gojimmypi/IoT_BBQ/Assignments/images/missing_mcu_families.png

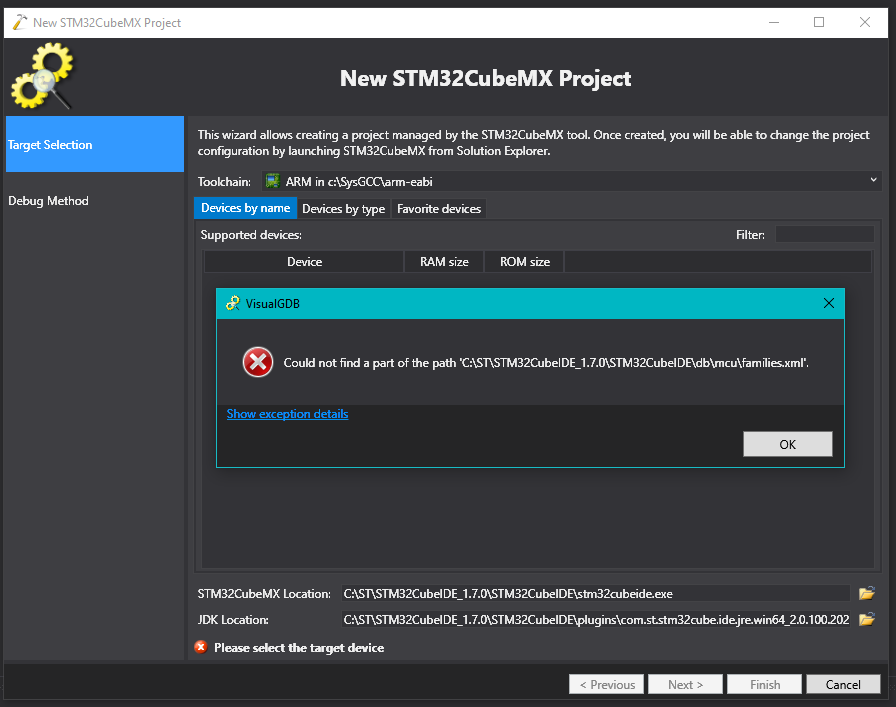
Assignments/images/missing_mcu_families.png
