gojimmypi/IoT_BBQ/pics/blinky_pins.png

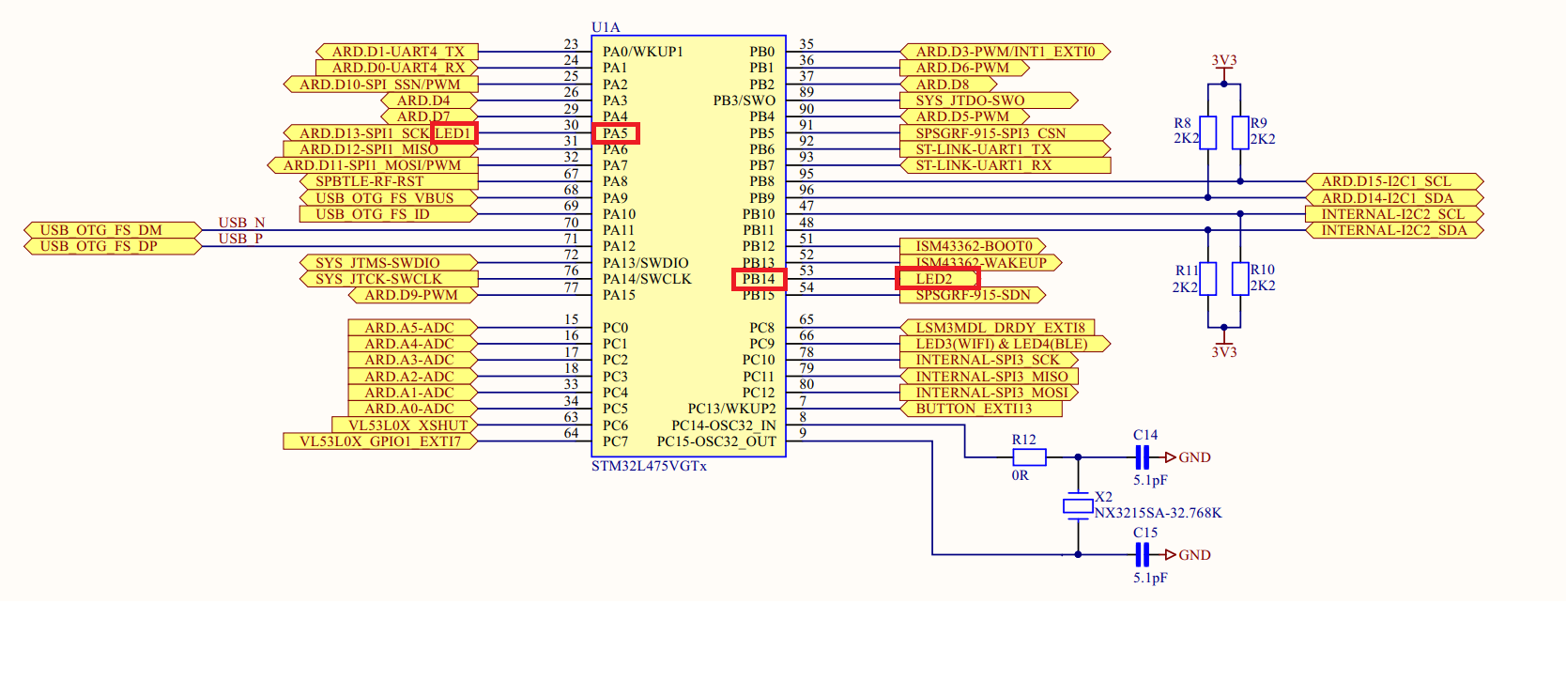
pics/blinky_pins.png
