gojimmypi/IoT_BBQ/pics/K-interface.jpg

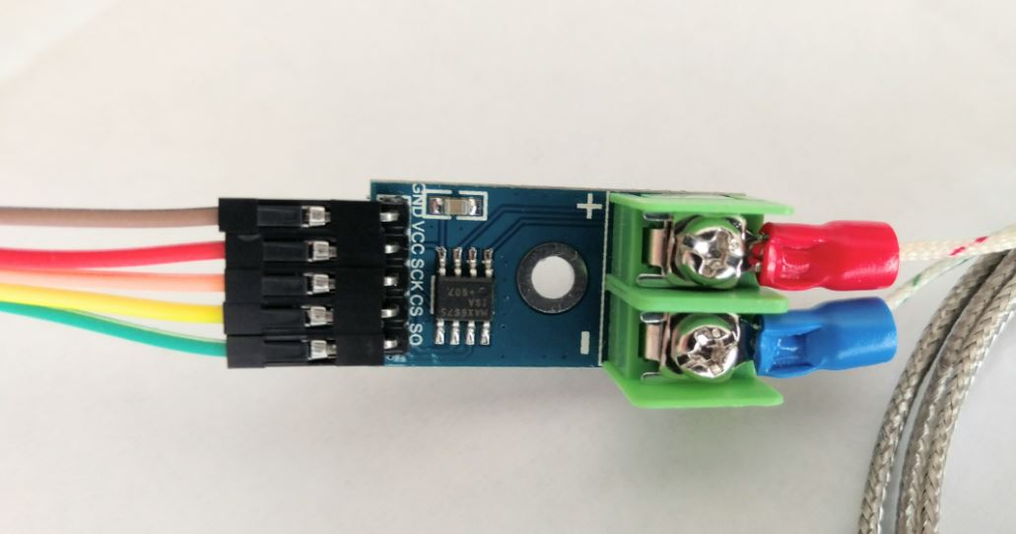
pics/K-interface.jpg
