gojimmypi/IoT_BBQ/IoT_BBQ_STM32/UART/UART.cpp

#include "../UART/UART.h"

#include <stm32l4xx_hal.h>
#include "int_to_string.h"


// #include <stm32_hal_legacy.h>

#ifdef __cplusplus
extern "C" {
#endif


    int UART_VERSION() {
        return 1;
    }



    //    void SysTick_Handler(void)
    //{
    //    HAL_IncTick();
    //    HAL_SYSTICK_IRQHandler();
    //}
    static UART_HandleTypeDef s_UARTHandle = UART_HandleTypeDef();
    SemaphoreHandle_t xUART_Semaphore = xSemaphoreCreateMutex();
    
    int UART_TxMessage(uint8_t *pData, uint16_t Size )
    {
        HAL_StatusTypeDef TxResult = HAL_OK;
        
        // see if our message is a zero terminated string, shorter than the max Size
        uint16_t FoundSize = Size;
        for (size_t i = 0; i < Size; i++)
        {
            if (pData[i] == 0)
            {
                FoundSize = i;
                break;
            }
        }

        if (xSemaphoreTake(xUART_Semaphore, (TickType_t) 10) == pdTRUE)
        {
            TxResult = HAL_UART_Transmit(&s_UARTHandle, pData, FoundSize, HAL_MAX_DELAY);
 
            /* We have finished accessing the shared resource.  Release the
            semaphore. */
            xSemaphoreGive(xUART_Semaphore);
        }
        else
        { 
            osDelay((TickType_t)(1000 / portTICK_PERIOD_MS));
            /* We could not obtain the semaphore and can therefore not access
            the shared resource safely. */
        }
        
        
        if(TxResult == HAL_OK)
        {
            return 0;
        }
        else
        {
            return TxResult;
        } 
            
    }

    const uint16_t NUM_STR_LEN = 32;
    int UART_TxMessageIntValue(uint8_t *pData, uint16_t Size, long Value)
    {
        //HAL_StatusTypeDef TxResult = HAL_UART_Transmit(&s_UARTHandle, pData, Size, HAL_MAX_DELAY);
        int TxResult = UART_TxMessage(pData, Size);
        if (TxResult == HAL_OK)
        {
            static char numStr[NUM_STR_LEN];
            int_to_dec(numStr, Value);
            UART_TxMessage((uint8_t*)numStr, 32);

            return 0;
        }
        else
        {
            return TxResult;
        } 
    }

    int UART_TxMessageIntValueHex(uint8_t *pData, uint16_t Size, long Value)
    {
        //HAL_StatusTypeDef TxResult = HAL_UART_Transmit(&s_UARTHandle, pData, Size, HAL_MAX_DELAY);
        int TxResult = UART_TxMessage(pData, Size);
        if (TxResult == HAL_OK)
        {
            static char numStr[NUM_STR_LEN];

            int_to_hex(numStr, Value);
            UART_TxMessage((uint8_t*)numStr, 32);
            return 0;
        }
        else
        {
            return TxResult;
        } 
    }
    

    int UART_init(void)
    {
        s_UARTHandle = UART_HandleTypeDef();

        __UART4_CLK_ENABLE();
        __GPIOA_CLK_ENABLE();

        GPIO_InitTypeDef GPIO_InitStructure;

        GPIO_InitStructure.Pin = GPIO_PIN_1;
        GPIO_InitStructure.Mode = GPIO_MODE_AF_PP;
        GPIO_InitStructure.Alternate = GPIO_AF8_UART4;
        GPIO_InitStructure.Speed = GPIO_SPEED_HIGH;
        GPIO_InitStructure.Pull = GPIO_NOPULL;
        HAL_GPIO_Init(GPIOA, &GPIO_InitStructure);

        GPIO_InitStructure.Pin = GPIO_PIN_0;
        GPIO_InitStructure.Mode = GPIO_MODE_AF_OD;
        HAL_GPIO_Init(GPIOA, &GPIO_InitStructure);

        s_UARTHandle.Instance = UART4;
        s_UARTHandle.Init.BaudRate = 115200;
        s_UARTHandle.Init.WordLength = UART_WORDLENGTH_8B;
        s_UARTHandle.Init.StopBits = UART_STOPBITS_1;
        s_UARTHandle.Init.Parity = UART_PARITY_NONE;
        s_UARTHandle.Init.HwFlowCtl = UART_HWCONTROL_NONE;
        s_UARTHandle.Init.Mode = UART_MODE_TX_RX;

        if (HAL_UART_Init(&s_UARTHandle) != HAL_OK)
            asm("bkpt 255");
        
        return 0; // TODO catch errors. return non-zero value
    }

#ifdef __cplusplus
}
#endif    
