gojimmypi/IoT_BBQ/IoT_BBQ_STM32/DISPLAY/DISPLAY.h

// DISPLAY.h
#pragma once

#ifdef __cplusplus
extern "C" {
#endif

    int task_display_VERSION();
    

        
	int DISPLAY_VERSION();
    int DISPLAY_init(void);
    void DISPLAY_Thread1(void const* argument);


#ifdef __cplusplus
}
#endif     
