gojimmypi/IoT_BBQ/IoT_BBQ_STM32/wiring_shift.c

#include "Common/globals.h"

/*
  wiring_shift.c - shiftOut() function
  Part of Arduino - http://www.arduino.cc/

  Copyright (c) 2005-2006 David A. Mellis

  Adapted from https://github.com/arduino/ArduinoCore-avr/blob/9f8d27f09f3bbd1da1374b5549a82bda55d45d44/cores/arduino/wiring_shift.c
  by gojimmypi
  
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
  You should have received a copy of the GNU Lesser General
  Public License along with this library; if not, write to the
  Free Software Foundation, Inc., 59 Temple Place, Suite 330,
  Boston, MA  02111-1307  USA
*/

#include <sys/_stdint.h>
#include <stm32l4xx_hal.h>
#include "DWT_STM32_DELAY.h"

#define HIGH 0x1
#define LOW  0x0
#define LSBFIRST 0
#define MSBFIRST 1


// WARNING: wrap calling function in portENTER_CRITICAL / portEXIT_CRITICAL
uint8_t shiftIn(uint16_t dataPin, uint16_t clockPin, uint8_t bitOrder) {
    uint8_t value = 0;
    uint8_t i;
    static int TimingDelay = 1;
    for (i = 0; i < 8; ++i) {
        
        // clock high
        HAL_GPIO_WritePin(GPIOB, clockPin, GPIO_PIN_SET); // Clock = Gray //digitalWrite(clockPin, HIGH);
        DWT_Delay_us(1); // WARNING! Hard, non-RTOS Delay
        
        if (bitOrder == LSBFIRST)
        {
            value |= HAL_GPIO_ReadPin(GPIOA, dataPin) << i; //value |= digitalRead(dataPin) << i;
        }
        else 
        {
            value |= HAL_GPIO_ReadPin(GPIOA, dataPin)  << (7 - i);
        }
        
        // clock low
        HAL_GPIO_WritePin(GPIOB, clockPin, GPIO_PIN_RESET); // digitalWrite(clockPin, LOW);
        DWT_Delay_us(1); // WARNING! Hard, non-RTOS Delay
    }
    return value;
}

GPIO_PinState PinStateOf(int v)
{
    if (v == 0)
    {
        return GPIO_PIN_RESET;
    }
    else
    {
        return GPIO_PIN_SET ;
    }
}

void shiftOut(uint16_t dataPin, uint16_t clockPin, uint8_t bitOrder, uint8_t val)
{
    uint8_t i;

    for (i = 0; i < 8; i++) {
        if (bitOrder == LSBFIRST) {
            // digitalWrite(dataPin, val & 1);
            HAL_GPIO_WritePin(GPIOA, dataPin, PinStateOf(val & 1));
            val >>= 1;
        }
        else {	
            // digitalWrite(dataPin, (val & 128) != 0);
            HAL_GPIO_WritePin(GPIOA, dataPin, PinStateOf((val & 128) != 0));
            val <<= 1;
        }
		
        HAL_GPIO_WritePin(GPIOB, clockPin, GPIO_PIN_SET);   //digitalWrite(clockPin, HIGH);
        HAL_GPIO_WritePin(GPIOB, clockPin, GPIO_PIN_RESET); //digitalWrite(clockPin, LOW);	
    }
}
