gojimmypi/IoT_BBQ/IoT_BBQ_STM32/_Init/startup.cpp

#include "startup.h"

#include  "../HX711/HX711.h"

#ifdef __cplusplus
extern "C" {
#endif

    
    //    void SysTick_Handler()
    //    {
    //        return;
    //    }
#ifdef __cplusplus
}
#endif    
