gojimmypi/IoT_BBQ/IoT_BBQ_STM32/_Init/Init_GPIO.h

// Init_GPIO.h

#ifndef _Init_GPIO_h
#define _Init_GPIO_h

#ifdef __cplusplus
extern "C" {
#endif

	void ConfigureI2CPins();
	void ConfigureI2CPins2();

	void GPIO_init();


#ifdef __cplusplus
}
#endif    

#endif
